hugoescalpelo/Digital-Hybrid-Design-and-Sensor-Programming/3D printed parts/Moldes/Seguro bocina izquierda.SLDPRT

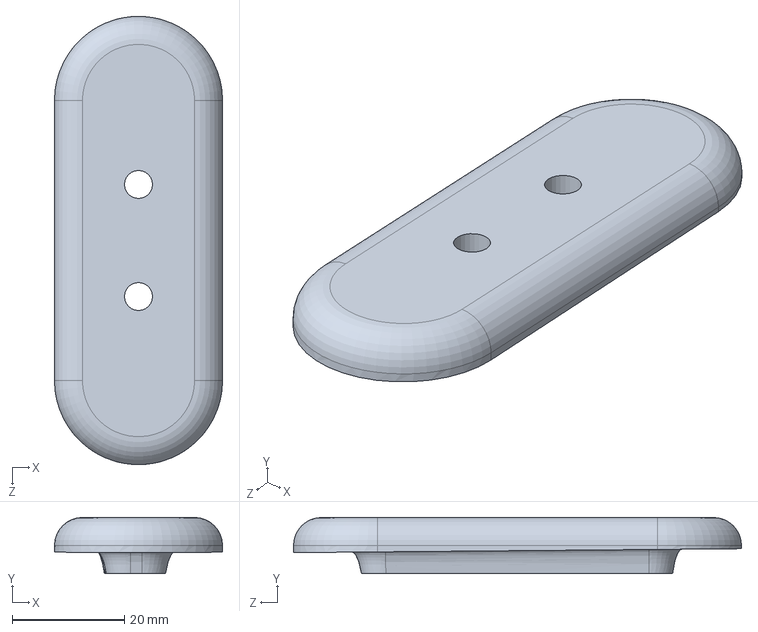
[picture p19: CAD file, 2021-03-20]
3D printed parts/Moldes/Seguro bocina izquierda.SLDPRT
30.0 x 10.0 x 79.9 mm
