hugoescalpelo/Digital-Hybrid-Design-and-Sensor-Programming/3D printed parts/Pecho/Part2.SLDPRT

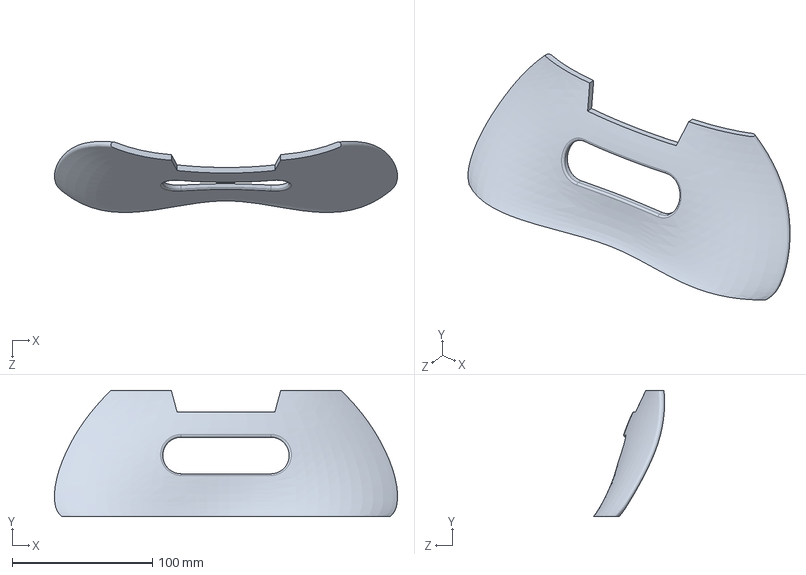
[picture p20: CAD file, 2021-03-20]
3D printed parts/Pecho/Part2.SLDPRT
244.5 x 90.0 x 50.7 mm
