hugoescalpelo/Digital-Hybrid-Design-and-Sensor-Programming/3D printed parts/Realsense/Realsense.SLDPRT

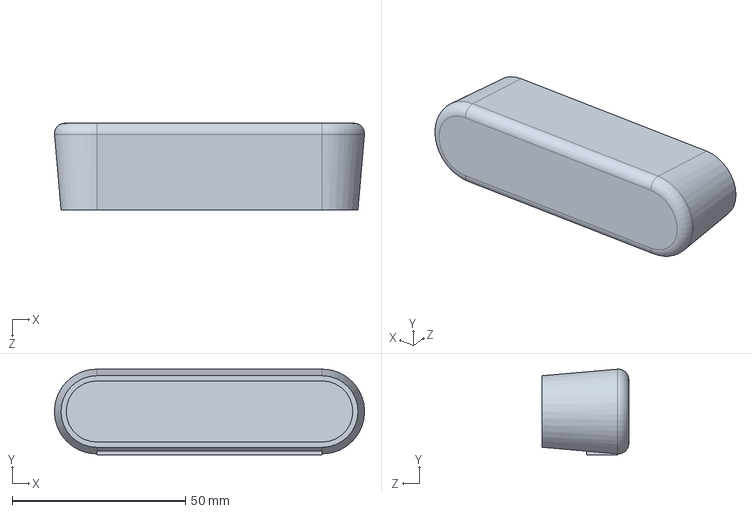
[picture p21: CAD file, 2021-03-20]
3D printed parts/Realsense/Realsense.SLDPRT
89.4 x 24.7 x 25.0 mm
