hugoescalpelo/Digital-Hybrid-Design-and-Sensor-Programming/3D printed parts/Union/Broche.SLDPRT

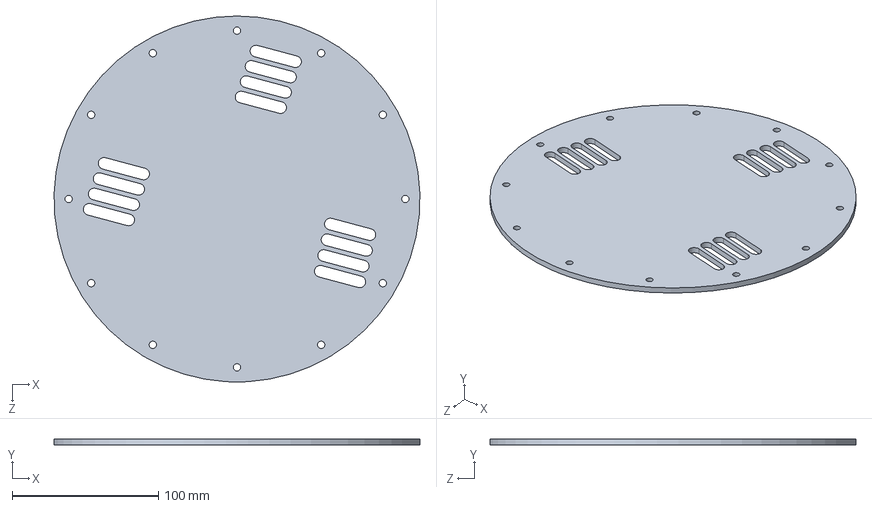
[picture p22: CAD file, 2021-03-20]
3D printed parts/Union/Broche.SLDPRT
249.9 x 4.00 x 250.0 mm
