hugoescalpelo/Digital-Hybrid-Design-and-Sensor-Programming/3D printed parts/Vertebra/Part1.SLDPRT

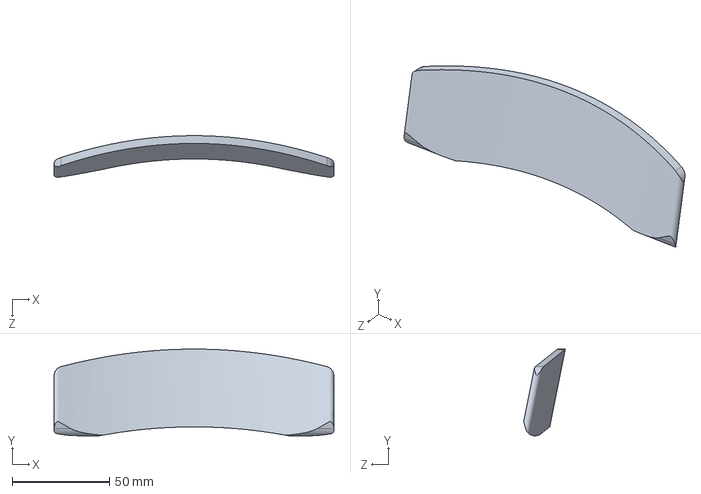
[picture p23: CAD file, 2021-03-20]
3D printed parts/Vertebra/Part1.SLDPRT
144.0 x 44.6 x 21.4 mm
