hugoescalpelo/Digital-Hybrid-Design-and-Sensor-Programming/Laser Cut/Disco.DXF

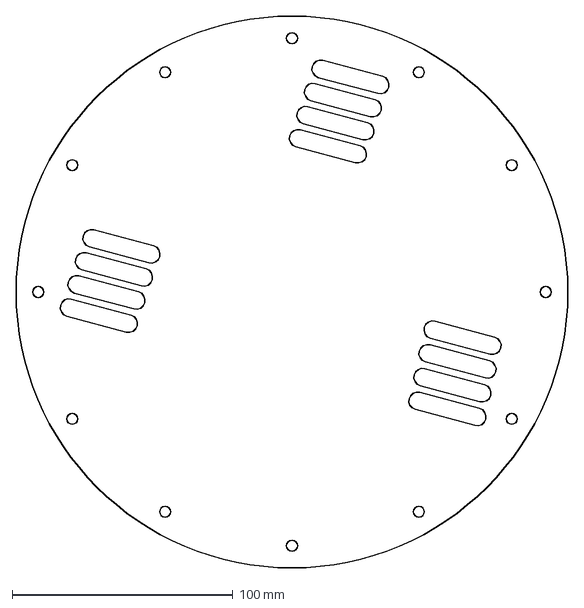
[picture p24: CAD file, 2021-03-20]
Laser Cut/Disco.DXF
250.0 x 250.0 mm
