hugoescalpelo/Digital-Hybrid-Design-and-Sensor-Programming/3D printed parts/Brazo/Brazo2.SLDPRT

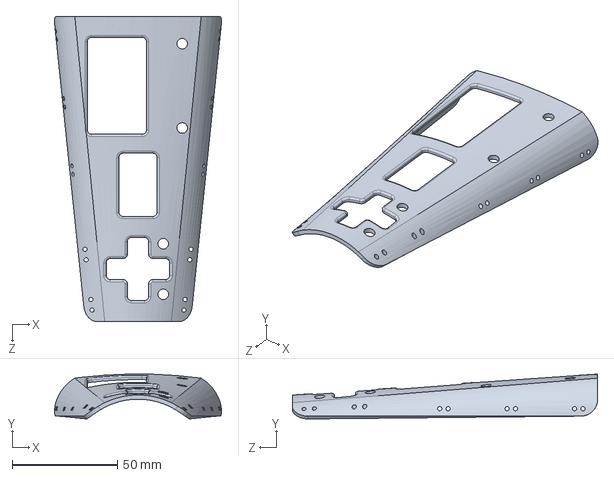
[picture p25: CAD file, 2021-03-20]
3D printed parts/Brazo/Brazo2.SLDPRT
79.3 x 21.3 x 145.0 mm
