hugoescalpelo/Digital-Hybrid-Design-and-Sensor-Programming/3D printed parts/Mini-o/Part2.SLDPRT

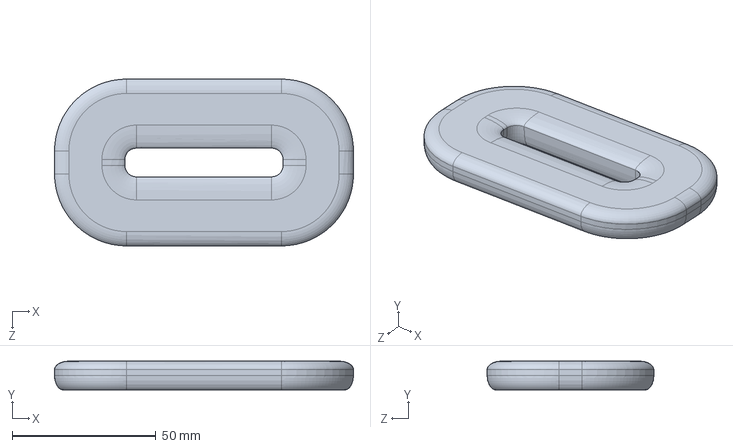
[picture p26: CAD file, 2021-03-20]
3D printed parts/Mini-o/Part2.SLDPRT
104.0 x 10.0 x 58.0 mm
