hugoescalpelo/Digital-Hybrid-Design-and-Sensor-Programming/3D printed parts/Pecho/Part1.SLDPRT

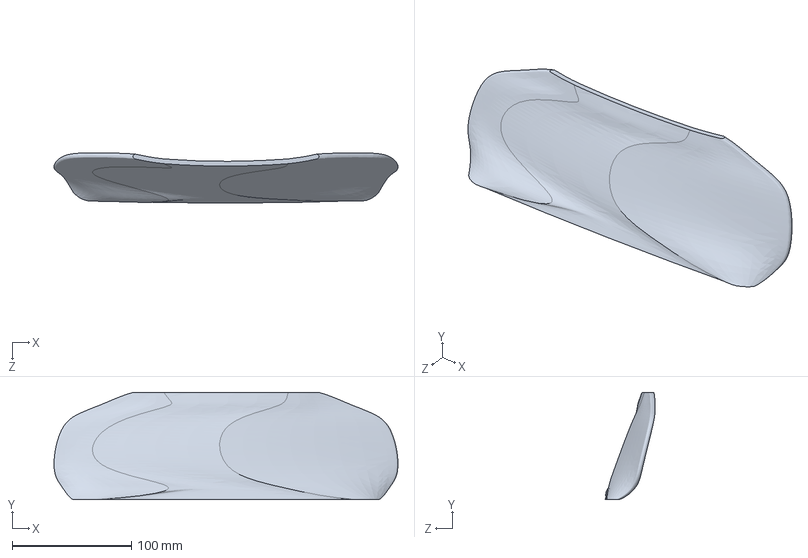
[picture p27: CAD file, 2021-03-20]
3D printed parts/Pecho/Part1.SLDPRT
288.6 x 90.0 x 42.1 mm
