hugoescalpelo/Digital-Hybrid-Design-and-Sensor-Programming/3D printed parts/Backpack/backpack 2d.SLDPRT

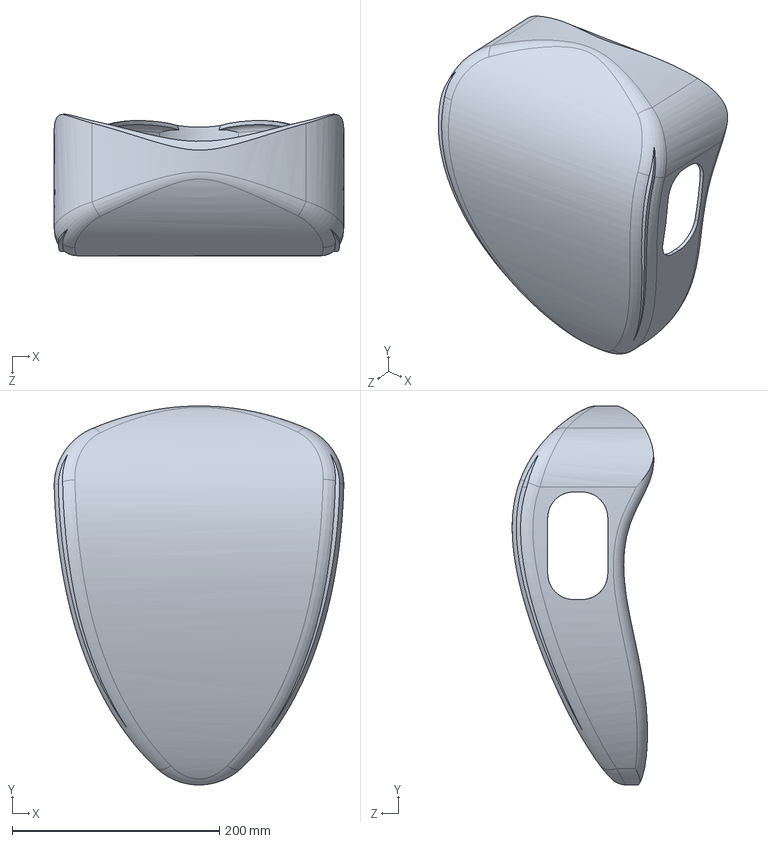
[picture p28: CAD file, 2021-03-20]
3D printed parts/Backpack/backpack 2d.SLDPRT
279.8 x 366.1 x 136.9 mm
