hugoescalpelo/Digital-Hybrid-Design-and-Sensor-Programming/3D printed parts/Jetson H/Separador.SLDPRT

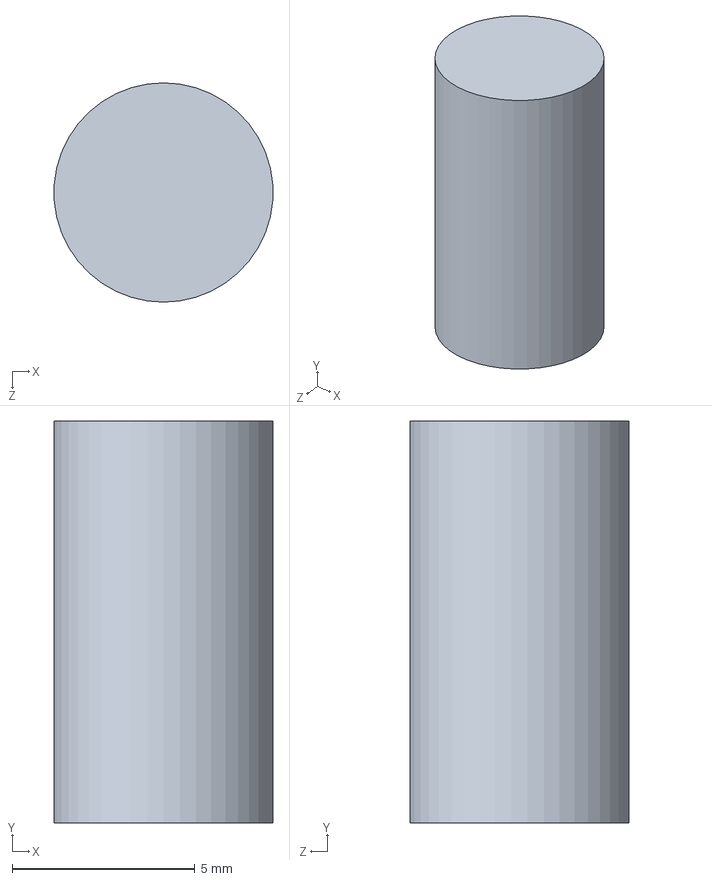
[picture p29: CAD file, 2021-03-20]
3D printed parts/Jetson H/Separador.SLDPRT
5.98 x 11.0 x 6.00 mm
