hugoescalpelo/Digital-Hybrid-Design-and-Sensor-Programming/3D printed parts/Pecho/Pecho.SLDPRT

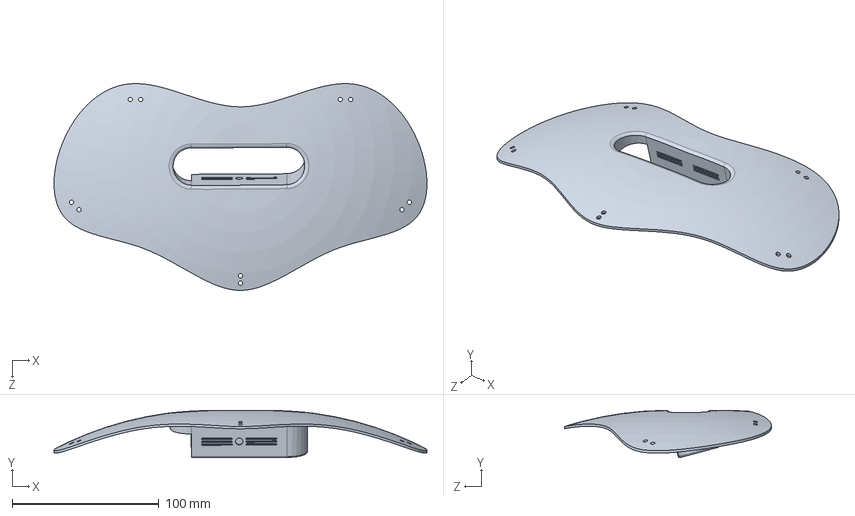
[picture p30: CAD file, 2021-03-20]
3D printed parts/Pecho/Pecho.SLDPRT
254.0 x 32.2 x 140.8 mm
