hugoescalpelo/Digital-Hybrid-Design-and-Sensor-Programming/3D printed parts/Realsense/Galss.SLDPRT

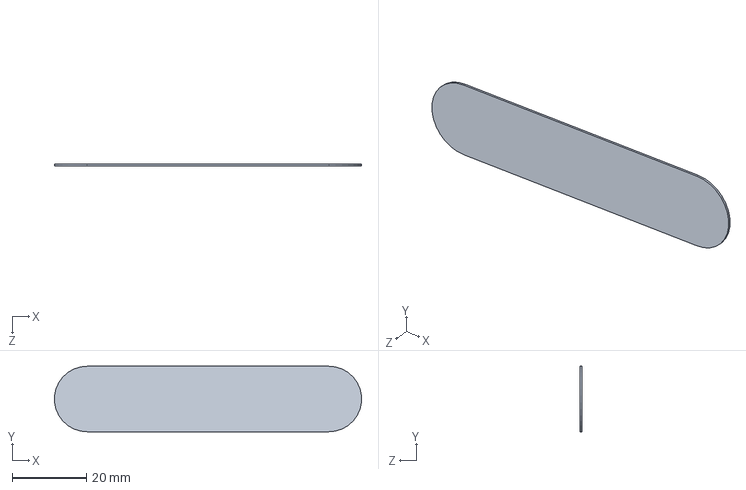
[picture p31: CAD file, 2021-03-20]
3D printed parts/Realsense/Galss.SLDPRT
82.5 x 17.6 x 0.5 mm
