hugoescalpelo/Digital-Hybrid-Design-and-Sensor-Programming/3D printed parts/Backpack/backpack 2c.SLDPRT

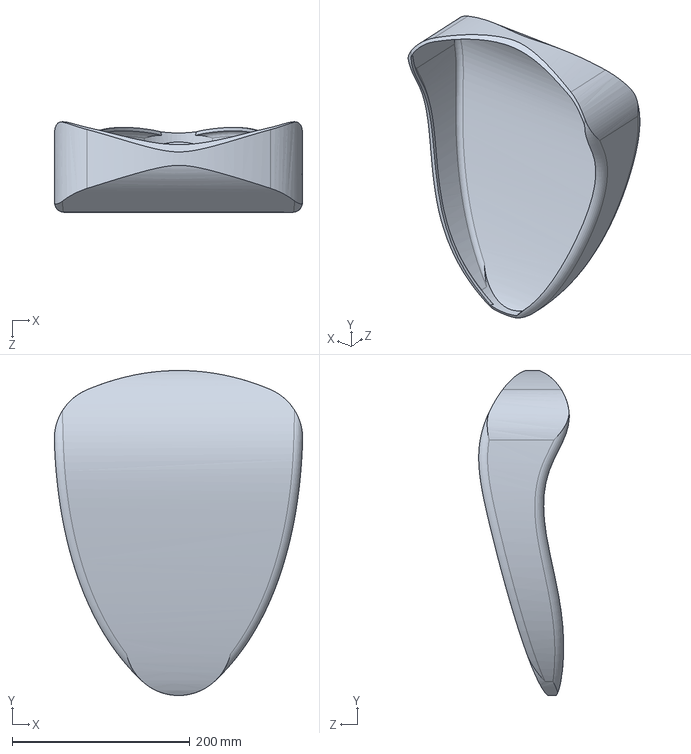
[picture p32: CAD file, 2021-03-20]
3D printed parts/Backpack/backpack 2c.SLDPRT
279.8 x 366.1 x 102.1 mm
