hugoescalpelo/Digital-Hybrid-Design-and-Sensor-Programming/3D printed parts/Jetson H/Base.SLDPRT

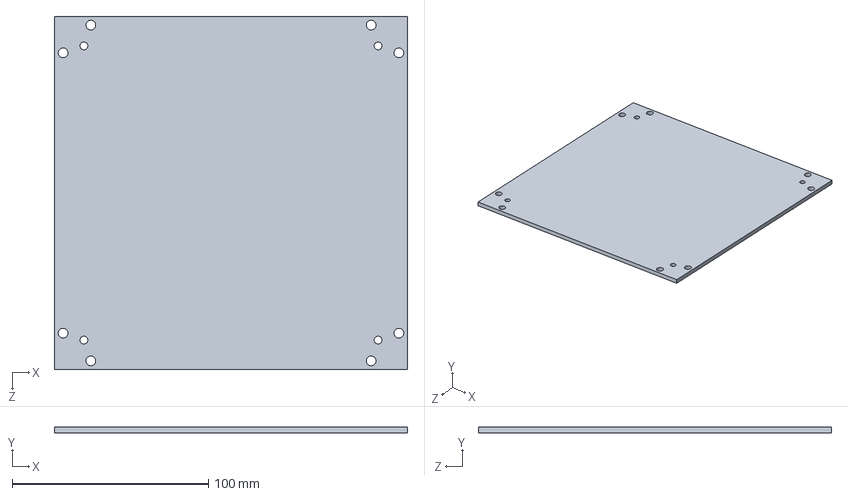
[picture p33: CAD file, 2021-03-20]
3D printed parts/Jetson H/Base.SLDPRT
180.0 x 3.00 x 180.0 mm
