hugoescalpelo/Digital-Hybrid-Design-and-Sensor-Programming/3D printed parts/Moldes/Pieza soporte bocina derecha.SLDPRT

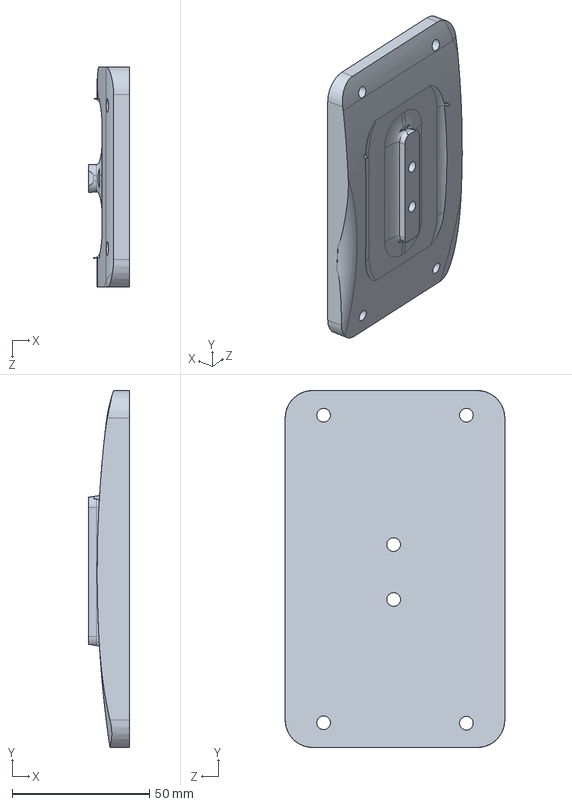
[picture p34: CAD file, 2021-03-20]
3D printed parts/Moldes/Pieza soporte bocina derecha.SLDPRT
15.0 x 130.0 x 80.0 mm
