hugoescalpelo/Digital-Hybrid-Design-and-Sensor-Programming/3D printed parts/Jetson H/Board.SLDPRT

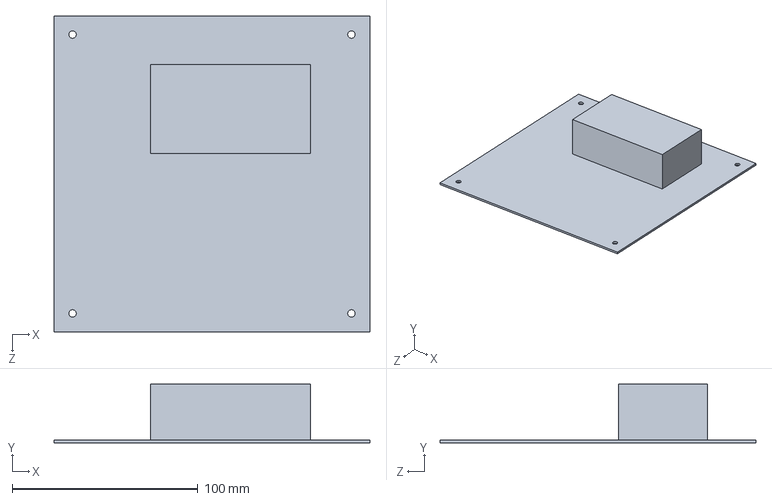
[picture p35: CAD file, 2021-03-20]
3D printed parts/Jetson H/Board.SLDPRT
170.0 x 31.5 x 170.0 mm
