hugoescalpelo/Digital-Hybrid-Design-and-Sensor-Programming/3D printed parts/Backpack/Part1.STL

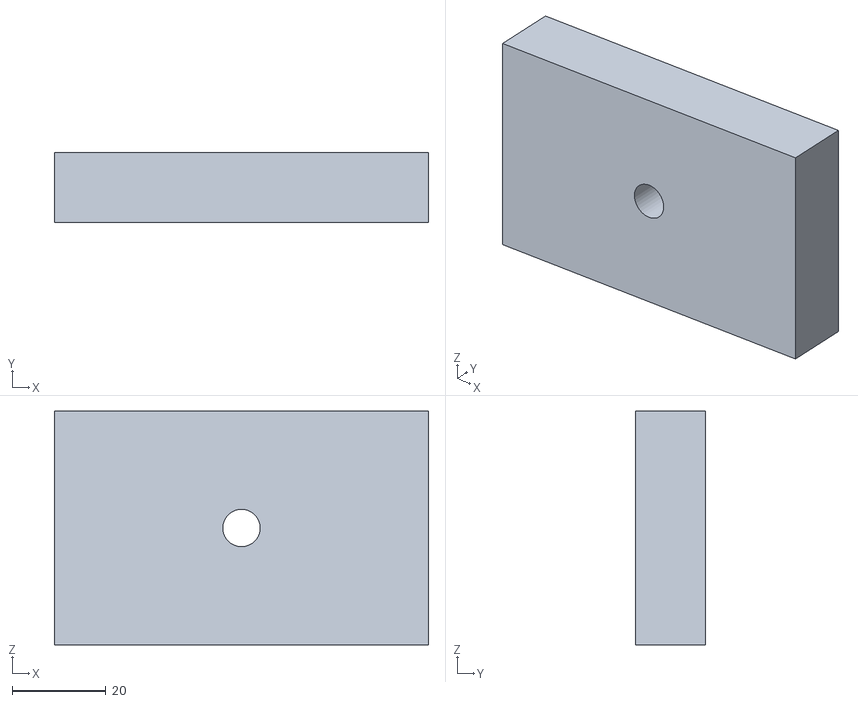
[picture p36: CAD file, 2021-03-20]
3D printed parts/Backpack/Part1.STL
80.0 x 15.0 x 50.0
