hugoescalpelo/Digital-Hybrid-Design-and-Sensor-Programming/3D printed parts/Backpack/BackPack Completo.STL

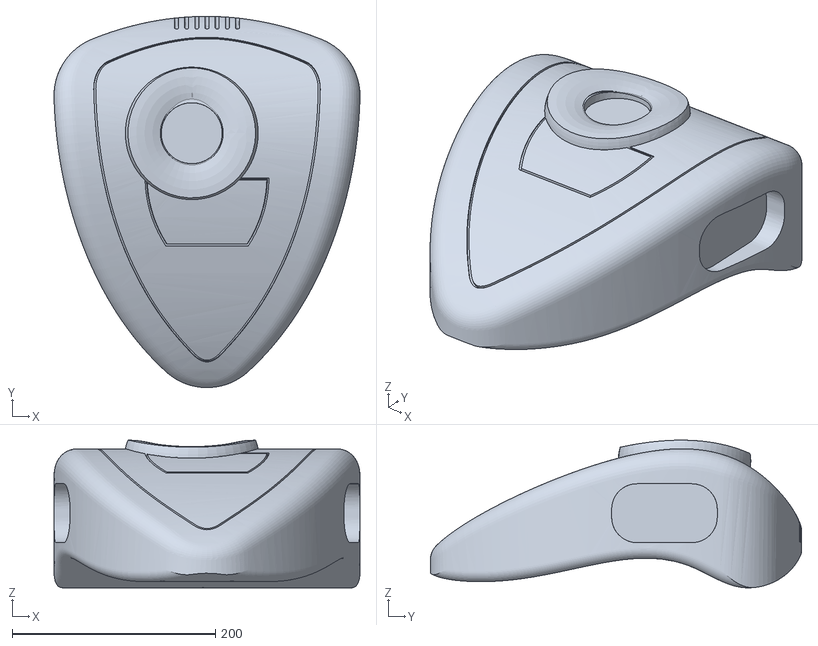
[picture p37: CAD file, 2021-03-20]
3D printed parts/Backpack/BackPack Completo.STL
301.2 x 365.4 x 145.5
