hugoescalpelo/Digital-Hybrid-Design-and-Sensor-Programming/3D printed parts/Backpack/Cubierta.SLDPRT

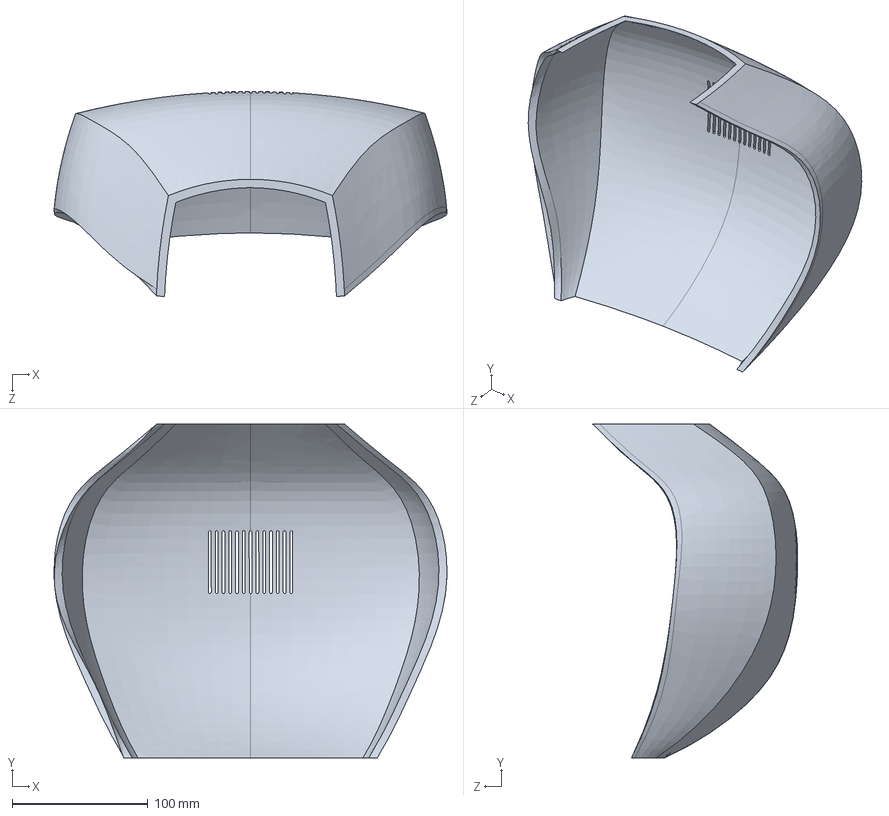
[picture p38: CAD file, 2021-03-20]
3D printed parts/Backpack/Cubierta.SLDPRT
289.3 x 245.9 x 151.3 mm
