hugoescalpelo/Digital-Hybrid-Design-and-Sensor-Programming/3D printed parts/Backpack/Backpack Completo + Base.STL

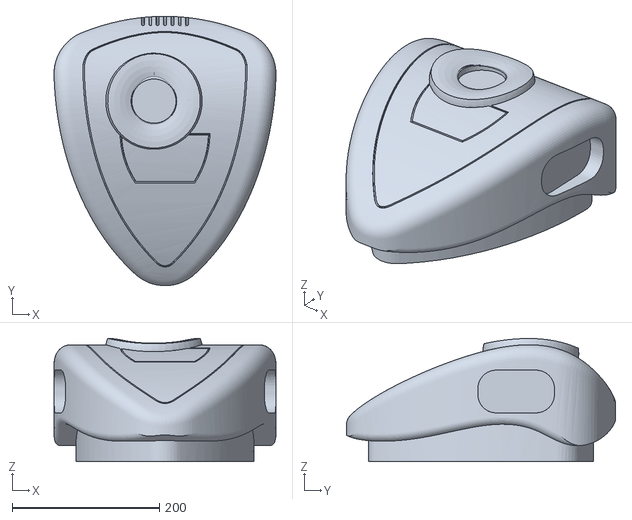
[picture p39: CAD file, 2021-03-20]
3D printed parts/Backpack/Backpack Completo + Base.STL
301.2 x 365.4 x 166.9
