hugoescalpelo/Digital-Hybrid-Design-and-Sensor-Programming/3D printed parts/Backpack/Molde.SLDPRT

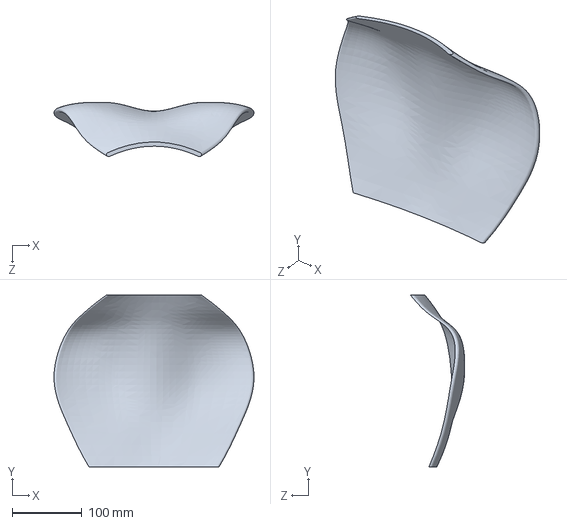
[picture p40: CAD file, 2021-03-20]
3D printed parts/Backpack/Molde.SLDPRT
286.1 x 245.9 x 77.8 mm
