hugoescalpelo/Digital-Hybrid-Design-and-Sensor-Programming/3D printed parts/Backpack/backpack 2g.SLDPRT

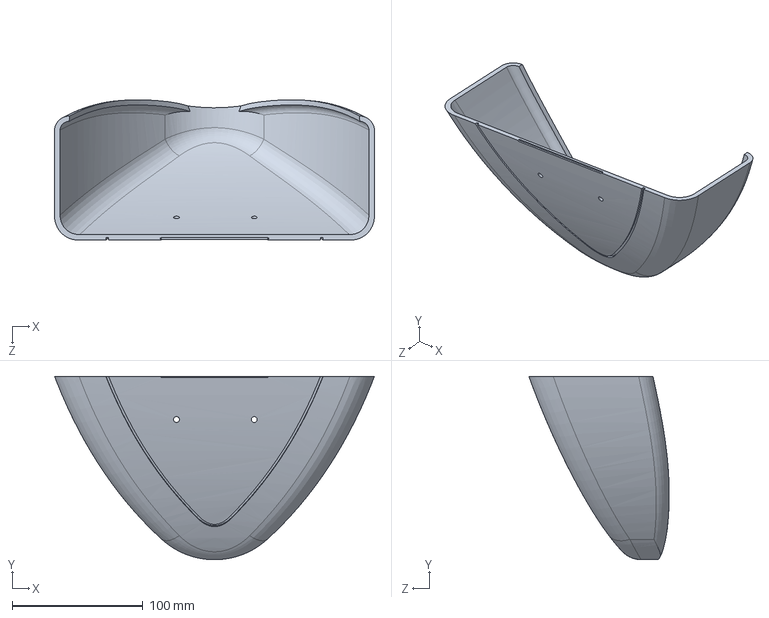
[picture p41: CAD file, 2021-03-20]
3D printed parts/Backpack/backpack 2g.SLDPRT
244.9 x 140.4 x 107.5 mm
