hugoescalpelo/Digital-Hybrid-Design-and-Sensor-Programming/3D printed parts/Backpack/backpack 2g mold1.SLDPRT

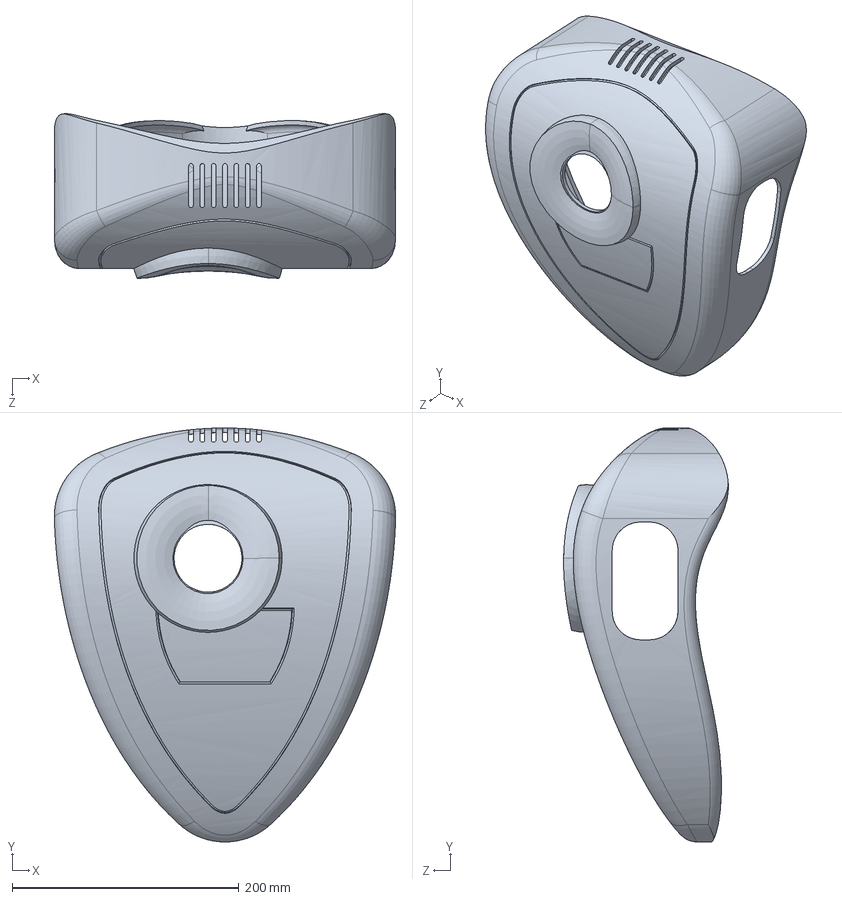
[picture p42: CAD file, 2021-03-20]
3D printed parts/Backpack/backpack 2g mold1.SLDPRT
301.2 x 365.4 x 145.4 mm
