hugoescalpelo/Digital-Hybrid-Design-and-Sensor-Programming/3D printed parts/Backpack/Union right.SLDPRT

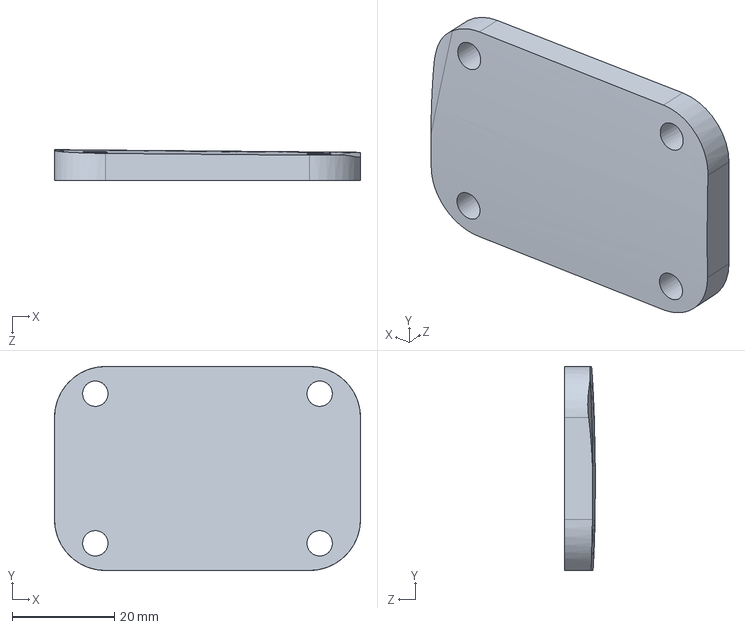
[picture p43: CAD file, 2021-03-20]
3D printed parts/Backpack/Union right.SLDPRT
60.0 x 40.0 x 6.03 mm
