hugoescalpelo/Digital-Hybrid-Design-and-Sensor-Programming/3D printed parts/Backpack/backpack 2b.SLDPRT

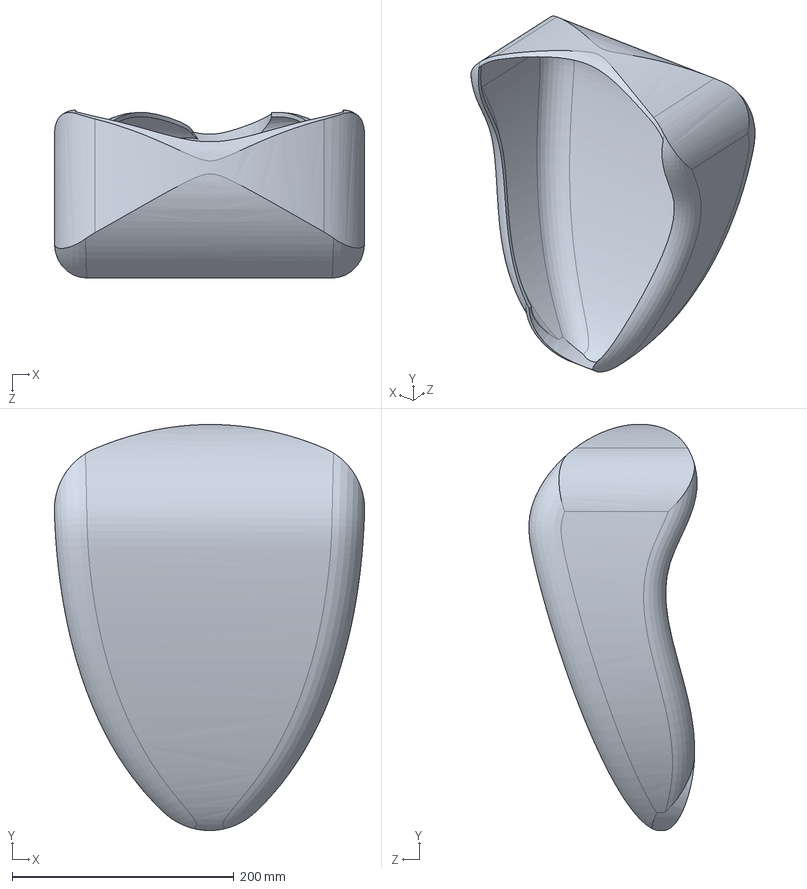
[picture p44: CAD file, 2021-03-20]
3D printed parts/Backpack/backpack 2b.SLDPRT
279.8 x 366.1 x 151.7 mm
